wa2ab1/DashMaster/Wiring/Wiring.kicad_sch

## KiCad design Wiring/Wiring.kicad_sch (2026-06-20)

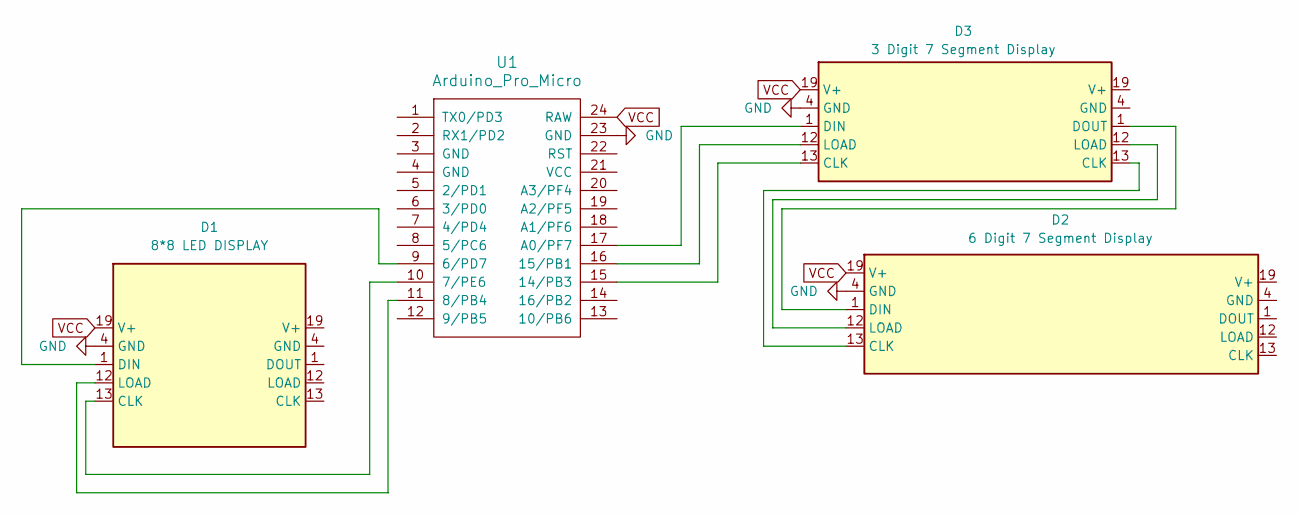
[picture p4: schematic Wiring.kicad_sch]

Parts:
D1: 8*8 LED DISPLAY
D2: 6 Digit 7 Segment Display
D3: 3 Digit 7 Segment Display
U1: Arduino_Pro_Micro

Connections:
GND: D1.4 (GND), D2.4 (GND), D3.4 (GND), U1.23 (GND)
unnamed: D1.1 (DIN), U1.9 (6/PD7)
unnamed: D1.12 (LOAD), U1.11 (8/PB4)
unnamed: D1.13 (CLK), U1.10 (7/PE6)
unnamed: D2.1 (DIN), D3.1 (DIN)
unnamed: D2.12 (LOAD), D3.12 (LOAD)
unnamed: D2.13 (CLK), D3.13 (CLK)
unnamed: D3.1 (DIN), U1.17 (A0/PF7)
unnamed: D3.12 (LOAD), U1.16 (15/PB1)
unnamed: D3.13 (CLK), U1.15 (14/PB3)
VCC: D1.19 (V+), D2.19 (V+), D3.19 (V+), U1.24 (RAW)
